jglim/OkayCAN/Firmware/Examples/OkayCAN_OBD/src/mainpage.h

#include "Arduino.h"

/*
	this contains the index web page. 
	the array can be generated easily in HxD : https://mh-nexus.de/en/hxd/
	open the html file in and choose Edit -> Copy as -> C
	then paste the content here and format it to fit

	[!] the actual html file is NOT included during the build process
	[!] ensure that there is a null terminator at the end of the page!
*/
const char mainpage_p[] PROGMEM = {

	0x3C, 0x21, 0x44, 0x4F, 0x43, 0x54, 0x59, 0x50, 0x45, 0x20, 0x68, 0x74,
	0x6D, 0x6C, 0x3E, 0x0D, 0x0A, 0x3C, 0x68, 0x74, 0x6D, 0x6C, 0x20, 0x6C,
	0x61, 0x6E, 0x67, 0x3D, 0x22, 0x65, 0x6E, 0x22, 0x3E, 0x0D, 0x0A, 0x0D,
	0x0A, 0x3C, 0x68, 0x65, 0x61, 0x64, 0x3E, 0x0D, 0x0A, 0x20, 0x20, 0x20,
	0x20, 0x3C, 0x6D, 0x65, 0x74, 0x61, 0x20, 0x63, 0x68, 0x61, 0x72, 0x73,
	0x65, 0x74, 0x3D, 0x22, 0x55, 0x54, 0x46, 0x2D, 0x38, 0x22, 0x3E, 0x0D,
	0x0A, 0x0D, 0x0A, 0x20, 0x20, 0x20, 0x20, 0x3C, 0x6D, 0x65, 0x74, 0x61,
	0x20, 0x68, 0x74, 0x74, 0x70, 0x2D, 0x65, 0x71, 0x75, 0x69, 0x76, 0x3D,
	0x22, 0x58, 0x2D, 0x55, 0x41, 0x2D, 0x43, 0x6F, 0x6D, 0x70, 0x61, 0x74,
	0x69, 0x62, 0x6C, 0x65, 0x22, 0x20, 0x63, 0x6F, 0x6E, 0x74, 0x65, 0x6E,
	0x74, 0x3D, 0x22, 0x49, 0x45, 0x3D, 0x65, 0x64, 0x67, 0x65, 0x22, 0x3E,
	0x0D, 0x0A, 0x20, 0x20, 0x20, 0x20, 0x3C, 0x6D, 0x65, 0x74, 0x61, 0x20,
	0x6E, 0x61, 0x6D, 0x65, 0x3D, 0x22, 0x76, 0x69, 0x65, 0x77, 0x70, 0x6F,
	0x72, 0x74, 0x22, 0x20, 0x63, 0x6F, 0x6E, 0x74, 0x65, 0x6E, 0x74, 0x3D,
	0x22, 0x77, 0x69, 0x64, 0x74, 0x68, 0x3D, 0x64, 0x65, 0x76, 0x69, 0x63,
	0x65, 0x2D, 0x77, 0x69, 0x64, 0x74, 0x68, 0x2C, 0x20, 0x69, 0x6E, 0x69,
	0x74, 0x69, 0x61, 0x6C, 0x2D, 0x73, 0x63, 0x61, 0x6C, 0x65, 0x3D, 0x31,
	0x2E, 0x30, 0x22, 0x3E, 0x0D, 0x0A, 0x20, 0x20, 0x20, 0x20, 0x3C, 0x74,
	0x69, 0x74, 0x6C, 0x65, 0x3E, 0x4F, 0x42, 0x44, 0x20, 0x43, 0x6F, 0x6E,
	0x73, 0x6F, 0x6C, 0x65, 0x3C, 0x2F, 0x74, 0x69, 0x74, 0x6C, 0x65, 0x3E,
	0x0D, 0x0A, 0x20, 0x20, 0x20, 0x20, 0x3C, 0x73, 0x74, 0x79, 0x6C, 0x65,
	0x3E, 0x0D, 0x0A, 0x20, 0x20, 0x20, 0x20, 0x20, 0x20, 0x20, 0x20, 0x3A,
	0x72, 0x6F, 0x6F, 0x74, 0x20, 0x7B, 0x0D, 0x0A, 0x20, 0x20, 0x20, 0x20,
	0x20, 0x20, 0x20, 0x20, 0x20, 0x20, 0x20, 0x20, 0x2D, 0x2D, 0x6D, 0x61,
	0x69, 0x6E, 0x2D, 0x62, 0x67, 0x2D, 0x63, 0x6F, 0x6C, 0x6F, 0x72, 0x3A,
	0x20, 0x23, 0x31, 0x31, 0x31, 0x3B, 0x0D, 0x0A, 0x20, 0x20, 0x20, 0x20,
	0x20, 0x20, 0x20, 0x20, 0x7D, 0x0D, 0x0A, 0x0D, 0x0A, 0x20, 0x20, 0x20,
	0x20, 0x20, 0x20, 0x20, 0x20, 0x68, 0x74, 0x6D, 0x6C, 0x20, 0x7B, 0x0D,
	0x0A, 0x20, 0x20, 0x20, 0x20, 0x20, 0x20, 0x20, 0x20, 0x20, 0x20, 0x20,
	0x20, 0x66, 0x6F, 0x6E, 0x74, 0x2D, 0x66, 0x61, 0x6D, 0x69, 0x6C, 0x79,
	0x3A, 0x20, 0x73, 0x61, 0x6E, 0x73, 0x2D, 0x73, 0x65, 0x72, 0x69, 0x66,
	0x3B, 0x0D, 0x0A, 0x20, 0x20, 0x20, 0x20, 0x20, 0x20, 0x20, 0x20, 0x7D,
	0x0D, 0x0A, 0x20, 0x20, 0x20, 0x20, 0x3C, 0x2F, 0x73, 0x74, 0x79, 0x6C,
	0x65, 0x3E, 0x0D, 0x0A, 0x0D, 0x0A, 0x3C, 0x2F, 0x68, 0x65, 0x61, 0x64,
	0x3E, 0x0D, 0x0A, 0x0D, 0x0A, 0x3C, 0x62, 0x6F, 0x64, 0x79, 0x3E, 0x0D,
	0x0A, 0x20, 0x20, 0x20, 0x20, 0x3C, 0x73, 0x70, 0x61, 0x6E, 0x3E, 0x4F,
	0x6B, 0x61, 0x79, 0x43, 0x41, 0x4E, 0x20, 0x44, 0x65, 0x62, 0x75, 0x67,
	0x3C, 0x2F, 0x73, 0x70, 0x61, 0x6E, 0x3E, 0x0D, 0x0A, 0x20, 0x20, 0x20,
	0x20, 0x3C, 0x70, 0x72, 0x65, 0x20, 0x69, 0x64, 0x3D, 0x22, 0x6A, 0x73,
	0x6F, 0x6E, 0x2D, 0x63, 0x6F, 0x6E, 0x74, 0x61, 0x69, 0x6E, 0x65, 0x72,
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

};
